ecopoesis/nek-type-a/body/build_data/left_top.dxf

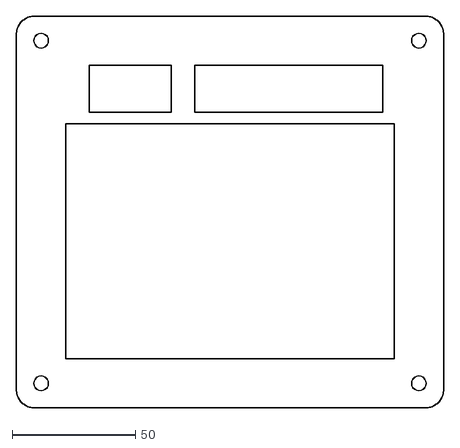
[picture p22: CAD file, 2018-05-13]
body/build_data/left_top.dxf
173.4 x 159.1
